turfptax/openmuscle/images/ESP32_S2_mini_V2-R6-02.jpg

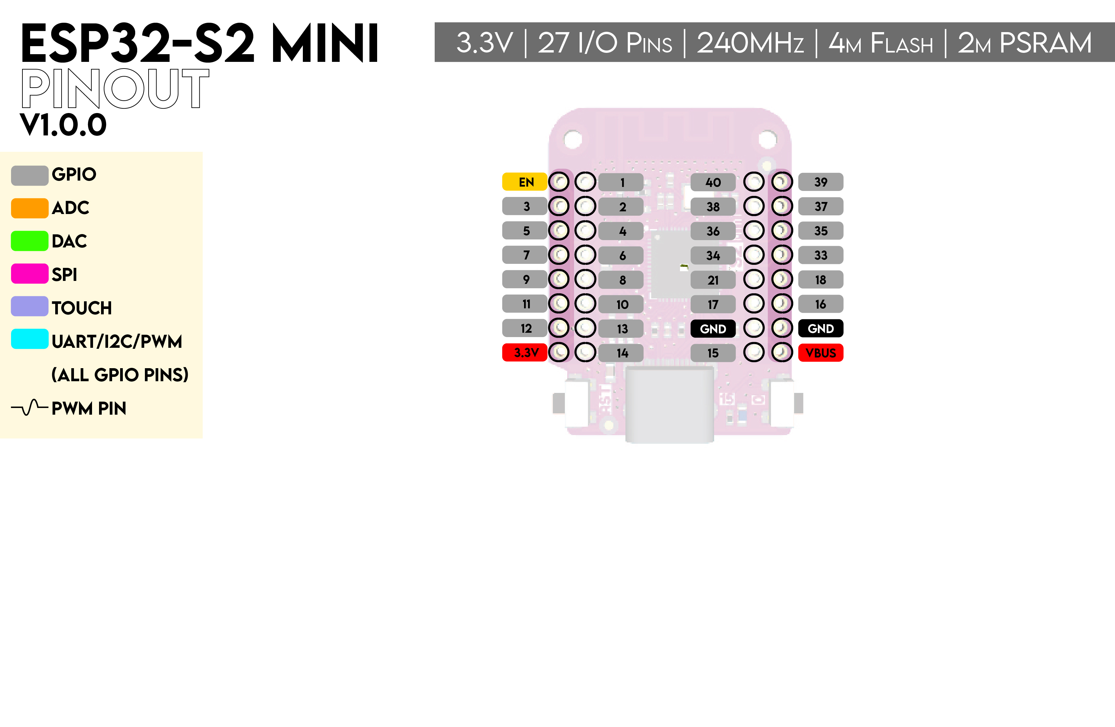
images/ESP32_S2_mini_V2-R6-02.jpg
