turfptax/openmuscle/images/OM-Band12 5-3-0-01.jpg

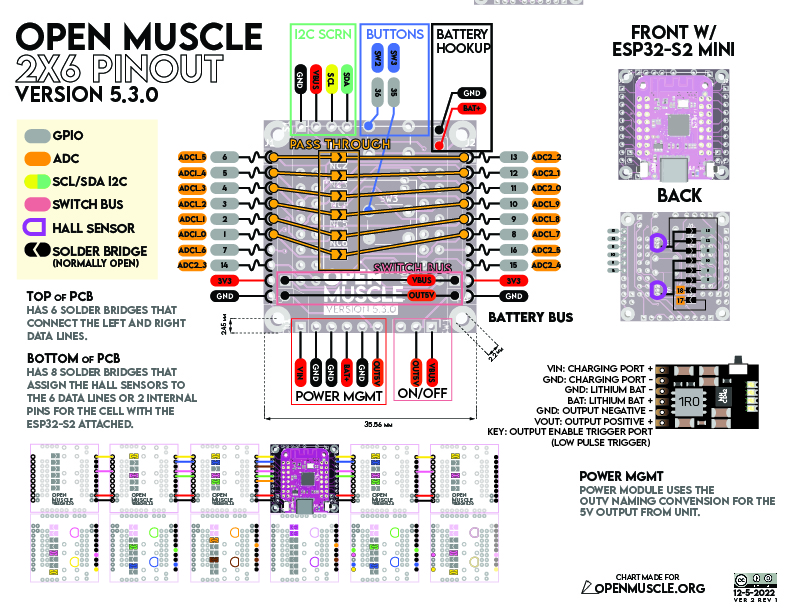
images/OM-Band12 5-3-0-01.jpg
