turfptax/openmuscle/images/Open Muscle 5-6 Foam Replacement.png

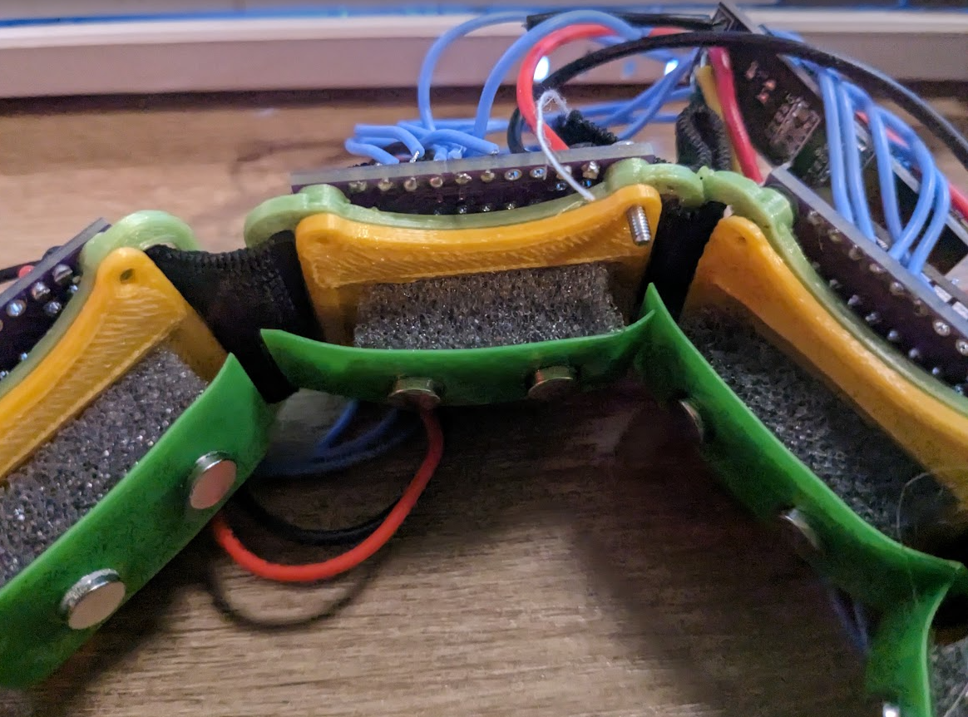
images/Open Muscle 5-6 Foam Replacement.png
