turfptax/openmuscle/images/Open-Muscle.png

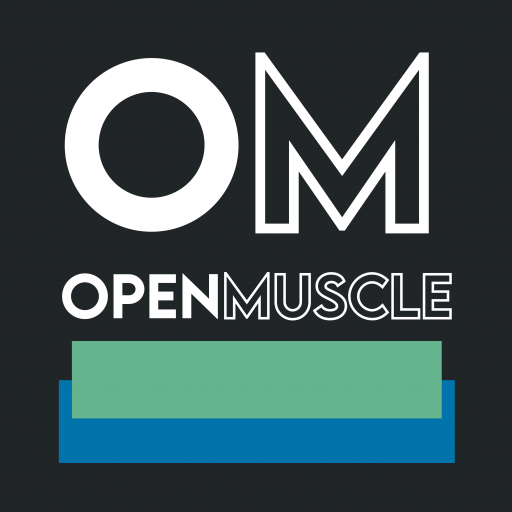
images/Open-Muscle.png
