turfptax/openmuscle/images/Predictions.png

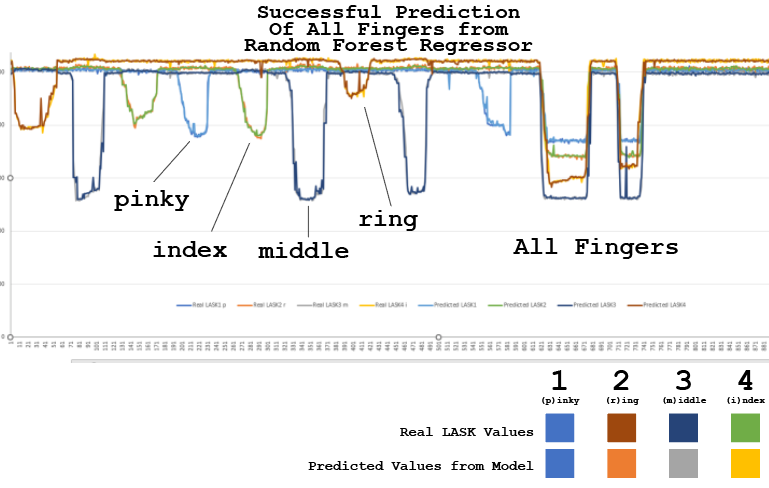
images/Predictions.png
