turfptax/openmuscle/images/Results-OM12-Jan-01.jpg

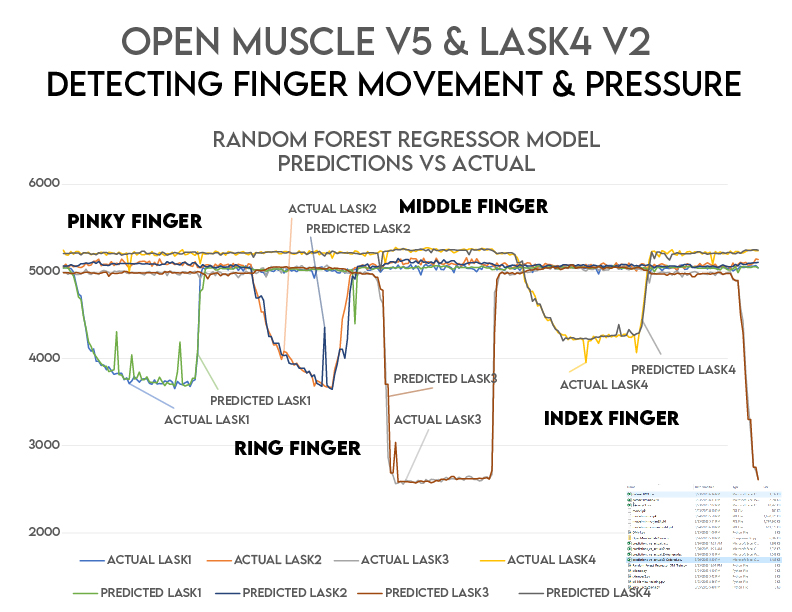
images/Results-OM12-Jan-01.jpg
